urjaman/wkdaywidget/timer.c

/*
 * Copyright (C) 2020 Urja Rannikko <urjaman@gmail.com>
 *
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
 */

#include "main.h"
#include "timer.h"
#include "buttons.h"
#include "rtc.h"

#define IDLE_TIMEOUT 600

/* This part is the non-calendar/date/time-related part. Just uptimer, etc. */
uint8_t timer_waiting=0;
static uint8_t timer_1hzp=0; // 1 HZ Pulse, 0/1
static uint8_t timer_5hzp=0; // 5 HZ Pulse
static uint32_t secondstimer=0;
static uint8_t timer5hz=0; // Linear 8-bit counter at 5hz, rolls over every 51s.
static uint8_t timer5hz_todo=0; // Used to fix linear counter if a 5hz pulse is missed.

/* Simplified "power management" code because we can never deep sleep. */
/* (Due to the timer PWMs being always on, because the display is always lit.) */
static void low_power_mode(void) {
	cli();
	SMCR = _BV(SE);
	sei();
	sleep_cpu();
	SMCR = 0; /* sleep_disable */
}


static uint16_t timer_gen_5hzp(void) {
	static uint8_t state=0;
	timer_5hzp=0;
	if (timer_1hzp) {
		state=0;
	}
	uint16_t rv;
	if ((rv=timer_get_lin_ss_u16())>=((SSTC/5)*state)) {
		timer_5hzp=1;
		state++;
	}
	return rv;
}

void timer_delay_us(uint24_t us) {
	uint24_t ss_start = timer_get_linear_ss_time();
	if (us>200000) us = 200000; // Safety Limit for 5hzP
	uint24_t ss_end = ss_start + (us/US_PER_SSUNIT) + 1;
	uint24_t ss_now;
	while ((ss_now=timer_get_linear_ss_time())<ss_end) {
		sleep_mode();
	}
}

void timer_delay_ms(uint8_t ms) {
	timer_delay_us((uint24_t)ms*1000);
}

void timer_set_waiting(void) {
	timer_waiting=1;
}

/* This is the interface from non-calendar time to calendar time functions. */
static void timer_time_tick();

void timer_run(void) {
	timer_1hzp=0;
	for (;;) {
		if (timer_getdec_todo()) {
			secondstimer++;
			timer_1hzp=1;
			timer5hz += timer5hz_todo;
			timer5hz_todo = 5;
			timer_time_tick();
		}

		timer_gen_5hzp();
		if (timer_5hzp) {
			timer5hz++;
			timer5hz_todo--;
		}
		if ((timer_5hzp)||(timer_1hzp)||(timer_waiting)||(buttons_get_v())) {
			timer_waiting=0;
			break;
		}
		low_power_mode();
	}
}


uint32_t timer_get(void) {
	return secondstimer;
}

uint8_t timer_get_1hzp(void) {
	return timer_1hzp;
}

uint8_t timer_get_5hzp(void) {
	return timer_5hzp;
}

uint8_t timer_get_5hz_cnt(void) {
	return timer5hz;
}

/*******************************************/
/* Here start the calendar time functions. */
/*******************************************/

// Time ticking without RTC is considered valid for this time.
#define TIME_NONRTC_VALID_TIME (6*60*60)

uint32_t timer_time_last_valid_moment=0;
uint8_t timer_time_valid=0;
static struct mtm timer_tm_now = { 0,1,1,0,0,0 };

void timer_set_time(struct mtm *tm) {
	timer_tm_now = *tm;
	timer_time_valid = 1;
	timer_time_last_valid_moment = secondstimer;
	rtc_write(tm); // If there is an RTC, set time into it.
}


void timer_get_time(struct mtm *tm) {
	*tm = timer_tm_now;
}

uint8_t timer_time_isvalid(void) {
	return timer_time_valid;
}

static void timer_time_tick(void) {
	uint8_t rv;
	struct mtm rtctime;
#if 1
	if ((rv=rtc_read(&rtctime))==0) { // We have RTC and it is valid, take it as the absolute truth.
		if ((timer_time_valid)&&(rtctime.year < timer_tm_now.year)) {
			/* Umm, no. */
			rv=2;
		} else {
			timer_tm_now = rtctime;
			timer_time_valid = 1;
			timer_time_last_valid_moment = secondstimer;
			return;
		}
	}
#endif

	// We have no RTC and have to wing it on our own.
	uint24_t tmp = timer_tm_now.sec+1;
	if (tmp>=60) {
		tmp = timer_tm_now.min+1;
		if (tmp>=60) {
			tmp = timer_tm_now.hour+1;
			if (tmp>=24) {
				tmp = mtm2lindate(&timer_tm_now)+1;
				lindate2mtm(&timer_tm_now,tmp);
				tmp = 0;
			}
			timer_tm_now.hour = tmp;
			tmp = 0;
		}
		timer_tm_now.min = tmp;
		tmp = 0;
	}
	timer_tm_now.sec = tmp;
	// Time incremented. Check if it is valid and whether it should still be valid.
	if (timer_time_valid) {
		uint32_t passed = secondstimer - timer_time_last_valid_moment;
		if (passed>TIME_NONRTC_VALID_TIME) timer_time_valid = 0;
	}
	if ((timer_time_valid)&&(rv==2)) { // RTC did exist but had no time, and our time is still valid, set RTC.
		rtc_write(&timer_tm_now);
	}
}
