urjaman/wkdaywidget/lang_en.h

#pragma once

#define WEEKDAYSTR "MOTUWETHFRSASU"

#define CENTURY_STR "Century: "
#define YEAR_STR "Year: "
#define MONTH_STR "Month: "
#define DAY_STR "Day: "
#define HOURS_STR "Hours: "
#define MINUTES_STR "Minutes: "
#define TIME_SET_DONE_STR "Time Set Done"

#define TIME_SET_STR "Time Set"
#define NIGHT_BR_SET_STR "Night Brightness Set"
#define DAY_BR_SET_STR "Day Brightness Set"
#define EXIT_STR "Quit Menu"

/* This in case we want to adjust behaviour otherwise based on the language, later. */
#define LANG_EN
