urjaman/wkdaywidget/lang_fi.h

#pragma once

#define WEEKDAYSTR "MATIKETOPELASU"

#define CENTURY_STR "Vuosisata: "
#define YEAR_STR "Vuosi: "
#define MONTH_STR "Kuukausi: "
#define DAY_STR "Paiva: "
#define HOURS_STR "Tunnit: "
#define MINUTES_STR "Minuutit: "
#define TIME_SET_DONE_STR "Aika Asetettu"

#define TIME_SET_STR "Ajan Asetus"
#define NIGHT_BR_SET_STR "Yokirkkauden Asetus"
#define DAY_BR_SET_STR "Paivakirkkauden Asetus"
#define EXIT_STR "Poistu"

/* This in case we want to adjust behaviour otherwise based on the language, later. */
#define LANG_FI
